huyhoang-1501/Smart_Health_Monitoring/flowchart/Phone Number Management.png

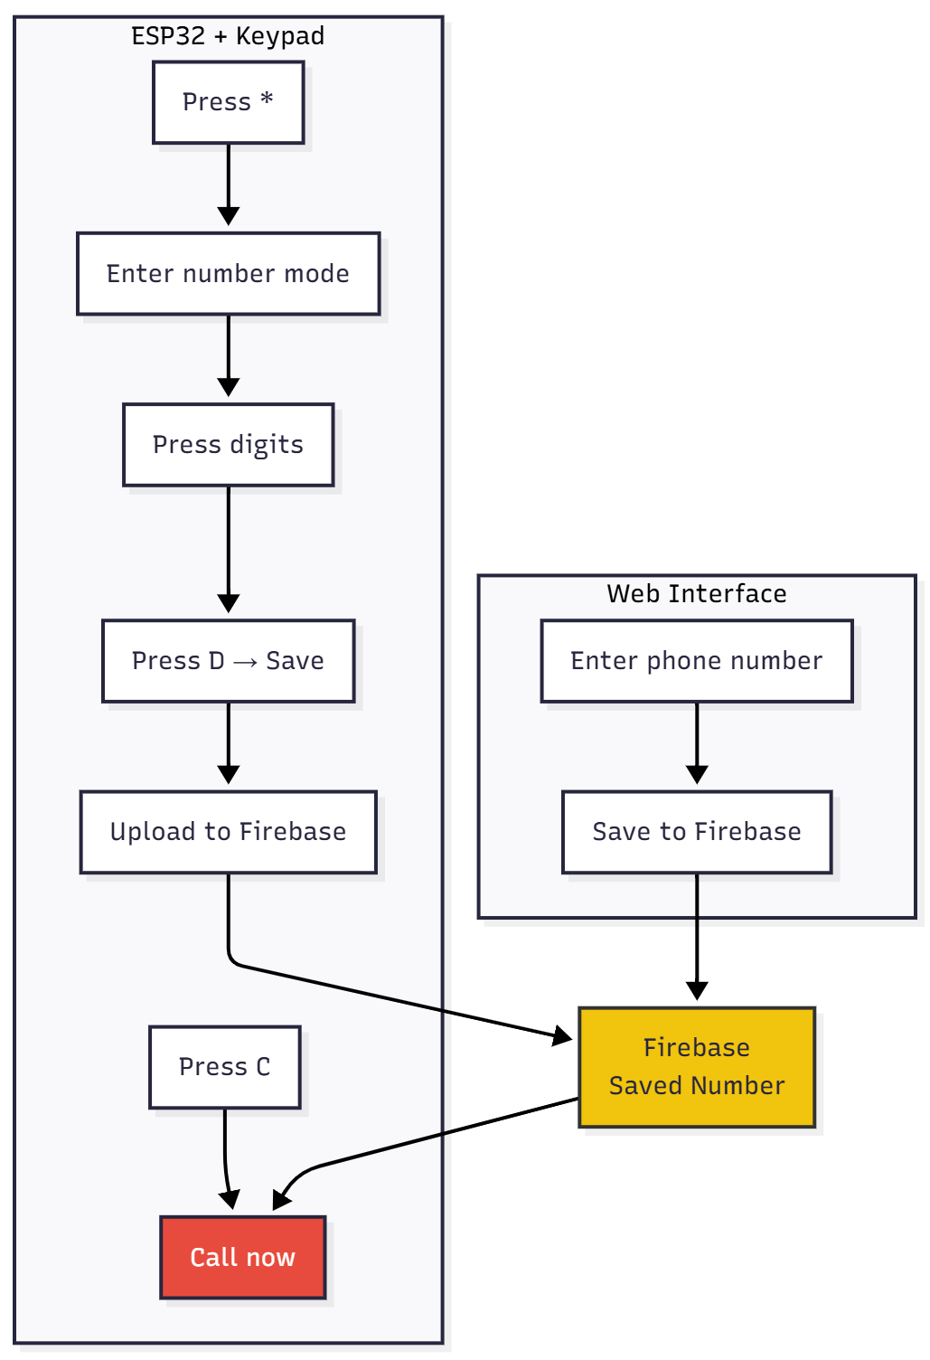
flowchart/Phone Number Management.png
