huyhoang-1501/Smart_Health_Monitoring/flowchart/Sensor Data Flow.png

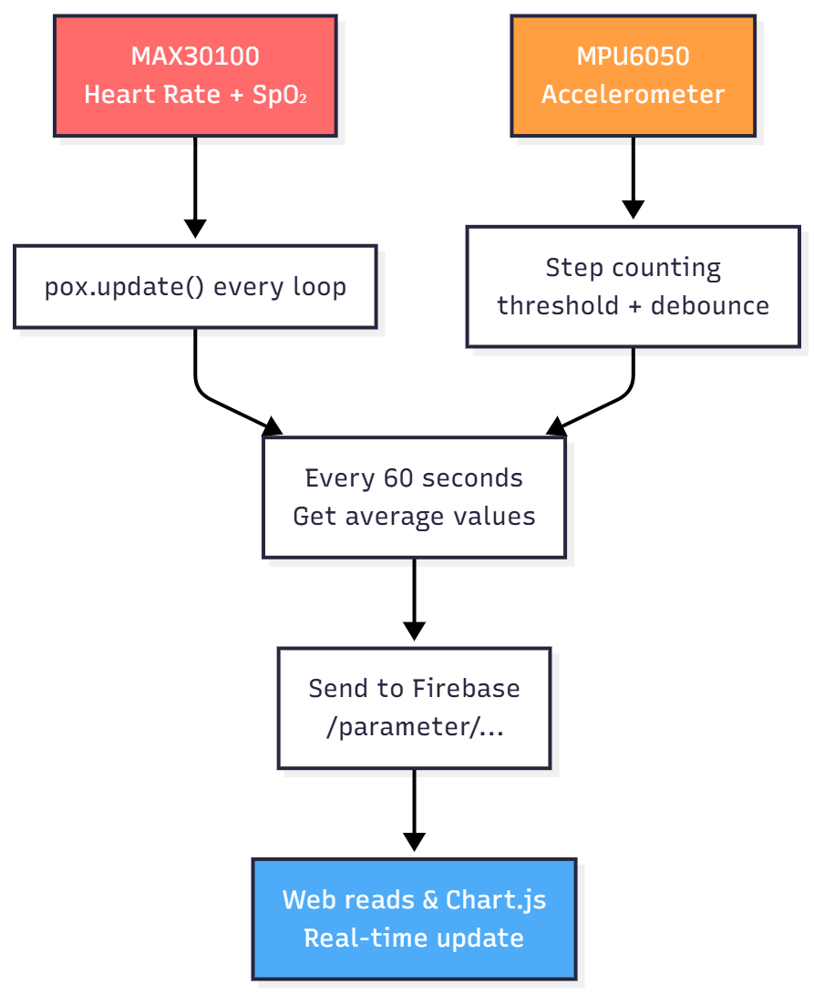
flowchart/Sensor Data Flow.png
