huyhoang-1501/Smart_Health_Monitoring/flowchart/Warning & Emergency Call Mechanism.png

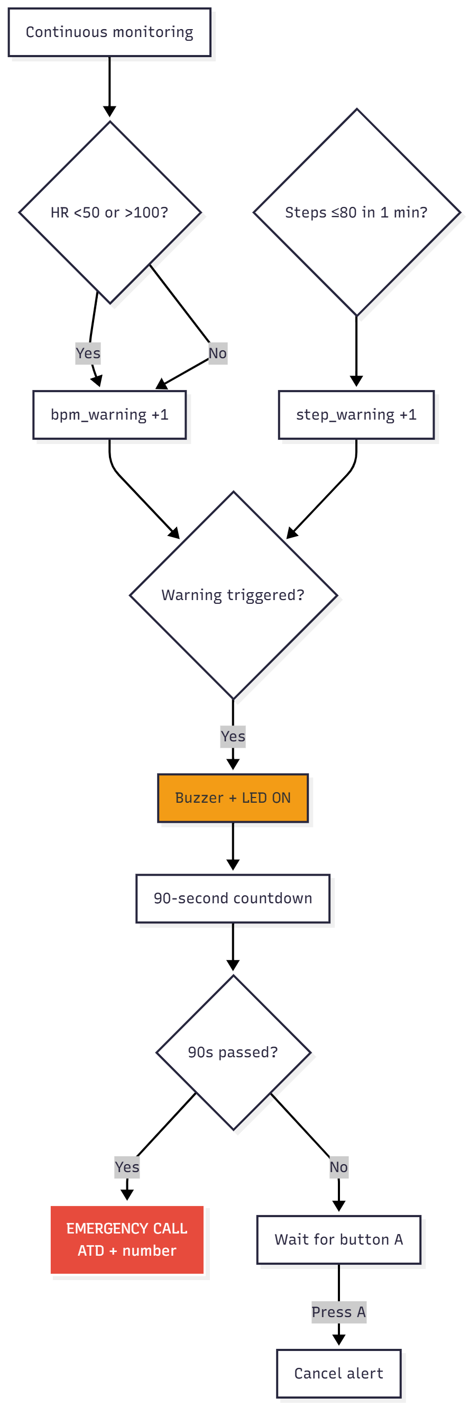
flowchart/Warning & Emergency Call Mechanism.png
